carrotIndustries/usbkvm/hw/usbkvm-pro/pool/3d_models/cache/6d752bc3-29b3-45df-8cf2-1e3aacefbcc6/3d_models/passive/capacitor/C_0402_1005Metric.step

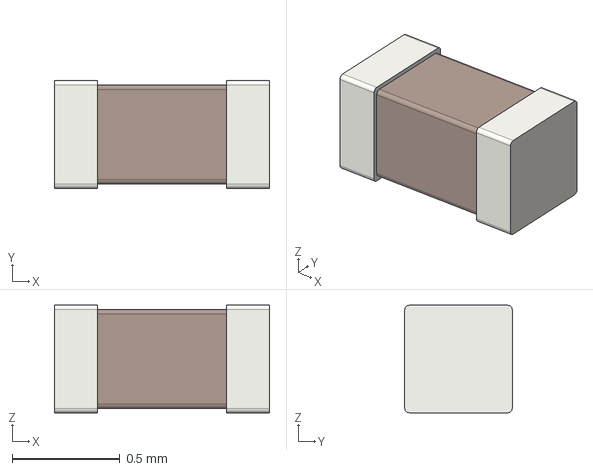
[picture p24: CAD file, 2024-03-15]
hw/usbkvm-pro/pool/3d_models/cache/6d752bc3-29b3-45df-8cf2-1e3aacefbcc6/3d_models/passive/capacitor/C_0402_1005Metric.step
1.00 x 0.5 x 0.5 mm
