carrotIndustries/usbkvm/hw/usbkvm-pro/pool/3d_models/cache/6d752bc3-29b3-45df-8cf2-1e3aacefbcc6/3d_models/passive/capacitor/C_0805_2012Metric.step

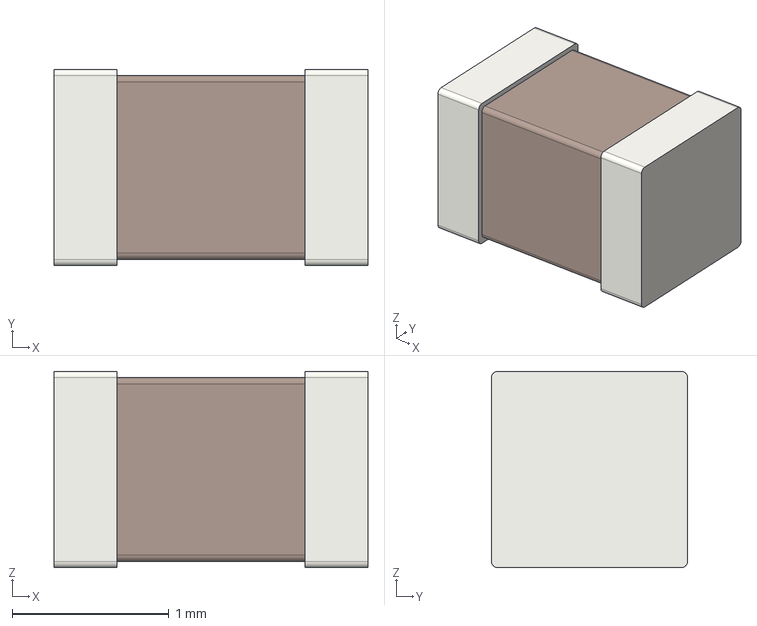
[picture p26: CAD file, 2024-03-15]
hw/usbkvm-pro/pool/3d_models/cache/6d752bc3-29b3-45df-8cf2-1e3aacefbcc6/3d_models/passive/capacitor/C_0805_2012Metric.step
2.00 x 1.25 x 1.25 mm
