carrotIndustries/usbkvm/hw/usbkvm-pro/pool/3d_models/cache/6d752bc3-29b3-45df-8cf2-1e3aacefbcc6/3d_models/ic/so/SOT-363_SC-70-6.step

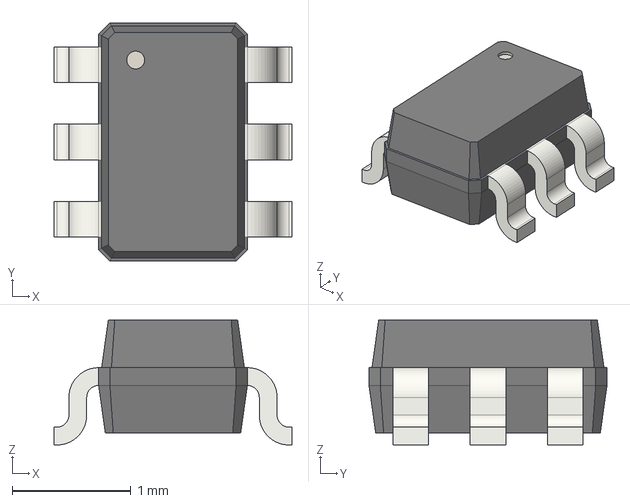
[picture p27: CAD file, 2024-03-15]
hw/usbkvm-pro/pool/3d_models/cache/6d752bc3-29b3-45df-8cf2-1e3aacefbcc6/3d_models/ic/so/SOT-363_SC-70-6.step
2.00 x 2.00 x 1.05 mm
