carrotIndustries/usbkvm/app/src/usbkvm_application.cpp

#include "usbkvm_application.hpp"
#include "main_window.hpp"
#include "about_dialog.hpp"
#include <iostream>
#include <hidapi.h>
#include "util.hpp"
#include "devices_window.hpp"

#ifndef G_OS_WIN32
#include <fcntl.h>
#include <linux/types.h>
#include <linux/input.h>
#include <linux/hidraw.h>
#endif

namespace usbkvm {

UsbKvmApplication::UsbKvmApplication() : Gtk::Application("net.carrotindustries.usbkvm", Gio::APPLICATION_FLAGS_NONE)
{
    add_main_option_entry(Gio::Application::OptionType::OPTION_TYPE_BOOL, "force-firmware-update", 0,
                          "Force firmware update regardless of detected version");
    add_main_option_entry(Gio::Application::OptionType::OPTION_TYPE_INT, "i2c-delay", 0,
                          "Min. I2C transaction interval in us");
    signal_handle_local_options().connect([this](const Glib::RefPtr<Glib::VariantDict> &dict) {
        bool force = false;
        dict->lookup_value("force-firmware-update", force);
        m_force_firmware_update = force;

        gint32 i2c_delay = 0;
        if (dict->lookup_value("i2c-delay", i2c_delay)) {
            if (i2c_delay == 1)
                i2c_delay = 0;
            m_i2c_delay_us = i2c_delay;
        }

        return -1;
    });
}

Glib::RefPtr<UsbKvmApplication> UsbKvmApplication::create()
{
    return Glib::RefPtr<UsbKvmApplication>(new UsbKvmApplication());
}

UsbKvmAppWindow *UsbKvmApplication::create_appwindow()
{
    auto appwindow = UsbKvmAppWindow::create(*this);

    // Make sure that the application runs for as long this window is still
    // open.
    add_window(*appwindow);

    // Gtk::Application::add_window() connects a signal handler to the window's
    // signal_hide(). That handler removes the window from the application.
    // If it's the last window to be removed, the application stops running.
    // Gtk::Window::set_application() does not connect a signal handler, but is
    // otherwise equivalent to Gtk::Application::add_window().

    // Delete the window when it is hidden.
    appwindow->signal_hide().connect(sigc::bind(sigc::mem_fun(*this, &UsbKvmApplication::on_hide_window), appwindow));

    return appwindow;
}

void UsbKvmApplication::on_activate()
{
    if (auto win = get_active_window()) {
        win->present();
        return;
    }
    auto appwindow = create_appwindow();
    appwindow->present();
}


void UsbKvmApplication::on_startup()
{
    // Call the base class's implementation.
    Gtk::Application::on_startup();

    add_action("quit", sigc::mem_fun(*this, &UsbKvmApplication::on_action_quit));
    add_action("about", sigc::mem_fun(*this, &UsbKvmApplication::on_action_about));
    add_action("devices", sigc::mem_fun(*this, &UsbKvmApplication::on_action_devices));

    auto cssp = Gtk::CssProvider::create();
    cssp->load_from_resource("/net/carrotIndustries/usbkvm/usbkvm.css");
    Gtk::StyleContext::add_provider_for_screen(Gdk::Screen::get_default(), cssp,
                                               GTK_STYLE_PROVIDER_PRIORITY_APPLICATION);
    Gtk::IconTheme::get_default()->add_resource_path("/net/carrotIndustries/usbkvm/icons");

    {
        m_monitor = gst_device_monitor_new();
        gst_device_monitor_set_show_all_devices(m_monitor, true);

        auto bus = gst_device_monitor_get_bus(m_monitor);
        gst_device_monitor_add_filter(m_monitor, "Video/Source", NULL);
        gst_bus_add_watch(bus, &UsbKvmApplication::monitor_bus_func, this);
        gst_object_unref(bus);
        gst_device_monitor_start(m_monitor);
    }

    Gtk::Settings::get_default()->property_gtk_menu_bar_accel() = "";

    m_devices_window = DevicesWindow::create(*this);

    signal_shutdown().connect(sigc::mem_fun(*this, &UsbKvmApplication::on_shutdown));
}


void UsbKvmApplication::on_shutdown()
{
    gst_device_monitor_stop(m_monitor);
    gst_object_unref(m_monitor);
    gst_deinit();
}

void UsbKvmApplication::on_hide_window(Gtk::Window *window)
{
    delete window;
}


void UsbKvmApplication::on_action_quit()
{
    // Gio::Application::quit() will make Gio::Application::run() return,
    // but it's a crude way of ending the program. The window is not removed
    // from the application. Neither the window's nor the application's
    // destructors will be called, because there will be remaining reference
    // counts in both of them. If we want the destructors to be called, we
    // must remove the window from the application. One way of doing this
    // is to hide the window. See comment in create_appwindow().
    auto windows = get_windows();
    for (auto win : windows)
        win->close();
}

void UsbKvmApplication::on_action_about()
{
    AboutDialog dia;
    auto win = get_active_window();
    if (win)
        dia.set_transient_for(*win);
    dia.run();
}

void UsbKvmApplication::on_action_devices()
{
    auto win = get_active_window();
    if (win)
        m_devices_window->set_transient_for(*win);
    m_devices_window->present();
}


gboolean UsbKvmApplication::monitor_bus_func(GstBus *bus, GstMessage *message, gpointer pself)
{
    auto self = reinterpret_cast<UsbKvmApplication *>(pself);
    return self->monitor_bus_func(bus, message);
}

static const std::string s_device_name = "USBKVM";

static std::string struct_get_string(const GstStructure *props, const char *name)
{
    if (auto r = gst_structure_get_string(props, name))
        return r;
    else
        return "";
}

struct OpenError : public std::runtime_error {
    using std::runtime_error::runtime_error;
};

#ifdef G_OS_WIN32

static std::string get_path(GstDevice *device)
{
    gchar *device_path;
    g_object_get(G_OBJECT(device), "path", &device_path, NULL);
    std::string r = device_path;
    g_free(device_path);
    return r;
}

static std::string get_hid_bus_info(const std::string &path)
{
    auto x = get_win32_hid_bus_info(path);
    if (x)
        return x.value();
    return "";
}

#else

static std::string get_hid_bus_info(const std::string &path)
{
    auto fd = open(path.c_str(), O_RDWR | O_NONBLOCK);
    if (fd == -1) {
        throw OpenError("can't open " + path + ", " + std::string(strerror(errno)));
        return "";
    }

    char buf[256] = {0};
    auto res = ioctl(fd, HIDIOCGRAWPHYS(256), buf);
    if (res < 0) {
        close(fd);
        return "";
    }
    else {
        close(fd);
        std::string buf_s = buf;
        auto slash_pos = buf_s.find('/');
        if (slash_pos == std::string::npos)
            return "";
        return buf_s.substr(0, slash_pos);
    }
}

static std::string get_path(GstDevice *device)
{
    auto props = gst_device_get_properties(device);
    auto path = struct_get_string(props, "device.path");
    if (!path.size())
        path = struct_get_string(props, "api.v4l2.path");
    gst_structure_free(props);
    return path;
}

#endif

static std::vector<gint> try_parse_dim(GstStructure *structure, const char *field)
{
    {
        int x;
        if (gst_structure_get_int(structure, field, &x))
            return {x};
    }
    {
        std::vector<gint> xs;
        GValueArray *array = nullptr;
        if (gst_structure_get_list(structure, field, &array)) {
            for (size_t i = 0; i < array->n_values; i++) {
                auto it = g_value_array_get_nth(array, i);
                if (it && G_VALUE_HOLDS(it, G_TYPE_INT)) {
                    auto x = g_value_get_int(it);
                    xs.push_back(x);
                }
            }
            g_value_array_free(array);
        }
        return xs;
    }
}

static gboolean handle_cap(GstCapsFeatures *features, GstStructure *structure, gpointer user_data)
{
    std::string name = gst_structure_get_name(structure);
    auto &ress = *(reinterpret_cast<DeviceInfo::ResolutionList *>(user_data));
    if (name == "image/jpeg") {
        std::vector<gint> widths, heights;
        widths = try_parse_dim(structure, "width");
        heights = try_parse_dim(structure, "height");
        for (const auto width : widths) {
            for (const auto height : heights) {
                ress.emplace_back(width, height);
            }
        }
    }
    return true;
}

const std::string UsbKvmApplication::s_recovery = "RECOVERY";


bool UsbKvmApplication::probe_device(const std::string &video_path, const std::string &video_bus_info,
                                     const DeviceInfo::ResolutionList &capture_resolutions)
{
    const auto recovery_mode = video_path == s_recovery;
    if (!recovery_mode) {
        if (!m_video_devices.contains(video_path))
            return false;
        {
            auto &x = m_video_devices.at(video_path);
            if (x++ == 10) {
                auto md = new Gtk::MessageDialog("Can't open HID interface", false, Gtk::MESSAGE_ERROR);
                md->set_secondary_text("didn't find HID device after one second", true);

                md->set_transient_for(*get_active_window());
                md->set_modal(true);
                md->present();
                md->signal_response().connect([md](auto response) { delete md; });
                return false;
            }
        }
    }

    auto devinfos = hid_enumerate(0x534d, 0x2109);
    bool found = false;
    for (const hid_device_info *dev = devinfos; dev != nullptr; dev = dev->next) {
        if (recovery_mode || (dev->product_string && wide_string_to_string(dev->product_string) == s_device_name)) {
            std::string hid_bus_info;
            try {
                hid_bus_info = get_hid_bus_info(dev->path);
            }
            catch (const OpenError &e) {
                auto md = new Gtk::MessageDialog("Can't open HID interface", false, Gtk::MESSAGE_ERROR);
                md->set_secondary_text(std::string(e.what()) + "\nSee <a href='https://github.com/carrotIndustries/usbkvm/blob/main/app/README.md'>github.com/carrotIndustries/usbkvm</a> for troubleshooting.", true);

                md->set_transient_for(*get_active_window());
                md->set_modal(true);
                md->present();
                md->signal_response().connect([md](auto response) { delete md; });
            }
            if (recovery_mode || hid_bus_info == video_bus_info) {
                on_device_added({.video_path = video_path,
                                 .hid_path = dev->path,
                                 .bus_info = hid_bus_info,
                                 .capture_resolutions = capture_resolutions});
                found = true;
                break;
            }
        }
    }
    hid_free_enumeration(devinfos);
    return !found;
}

gboolean UsbKvmApplication::monitor_bus_func(GstBus *bus, GstMessage *message)
{
    GstDevice *device;
    gchar *name;

    switch (GST_MESSAGE_TYPE(message)) {
    case GST_MESSAGE_DEVICE_ADDED: {
        gst_message_parse_device_added(message, &device);
        name = gst_device_get_display_name(device);
        g_print("Device added: %s\n", name);
        std::string name_str = name;
        if (name_str.starts_with(s_device_name)) {
            {
                DeviceInfo::ResolutionList capture_resolutions;
                {
                    auto caps = gst_device_get_caps(device);
                    gst_caps_foreach(caps, &handle_cap, &capture_resolutions);
                    gst_caps_unref(caps);
                }

                std::string video_path = get_path(device);
                std::string video_bus_info;
#ifdef G_OS_WIN32
                {
                    auto x = get_win32_video_bus_info(video_path);
                    if (x)
                        video_bus_info = x.value();
                }
#else
                auto props = gst_device_get_properties(device);
                video_bus_info = struct_get_string(props, "v4l2.device.bus_info");
                if (!video_bus_info.size())
                    video_bus_info = struct_get_string(props, "api.v4l2.cap.bus_info");
                gst_structure_free(props);
#endif

                if (video_path.size() && video_bus_info.size()) {
                    std::cout << "found video " << video_path << " at " << video_bus_info << std::endl;
                    if (m_video_devices.emplace(video_path, 0u).second) {
                        // give the HID device one second to appear
                        Glib::signal_timeout().connect(
                                [this, video_path, video_bus_info, capture_resolutions] {
                                    return probe_device(video_path, video_bus_info, capture_resolutions);
                                },
                                100);
                    }
                    else {
                        std::cout << "ignoring duplicate device " << video_path << std::endl;
                    }
                }
            }
        }
        g_free(name);
        gst_object_unref(device);
    } break;
    case GST_MESSAGE_DEVICE_REMOVED: {
        gst_message_parse_device_removed(message, &device);
        name = gst_device_get_display_name(device);
        auto path = get_path(device);
        std::string name_s = name;
        std::cout << "Device removed: " << name_s << " " << path << std::endl;
        m_video_devices.erase(path);
        on_device_removed(path);
        g_free(name);
        gst_object_unref(device);

    } break;
    default:
        break;
    }

    return G_SOURCE_CONTINUE;
}

void UsbKvmApplication::on_device_added(const DeviceInfo &devinfo)
{
    m_devices.emplace(devinfo.video_path, devinfo);
    m_signal_devices_changed.emit();
    // try to use last window
    for (auto win2 : get_windows()) {
        auto &win = dynamic_cast<UsbKvmAppWindow &>(*win2);
        if (win.get_device_info() == nullptr
            && (win.get_last_bus_info() == devinfo.bus_info || win.get_last_bus_info().empty())) {
            win.set_device(devinfo);
            return;
        }
    }
    // try any free window
    for (auto win2 : get_windows()) {
        auto &win = dynamic_cast<UsbKvmAppWindow &>(*win2);
        if (win.get_device_info() == nullptr) {
            win.set_device(devinfo);
            return;
        }
    }
    // no window, create new
    auto appwindow = create_appwindow();
    appwindow->set_device(devinfo);
    appwindow->present();
}

void UsbKvmApplication::on_device_removed(const std::string &video_path)
{
    for (auto win2 : get_windows()) {
        auto &win = dynamic_cast<UsbKvmAppWindow &>(*win2);
        if (auto info = win.get_device_info()) {
            if (info->video_path == video_path) {
                win.unset_device();
                break;
            }
        }
    }
    m_devices.erase(video_path);
    m_signal_devices_changed.emit();
}

void UsbKvmApplication::update_device_info(const DeviceInfo &info)
{
    if (m_devices.contains(info.video_path)) {
        auto &dev = m_devices.at(info.video_path);
        dev.model = info.model;
        dev.serial = info.serial;
        m_signal_devices_changed.emit();
    }
}

std::vector<const DeviceInfo *> UsbKvmApplication::get_devices() const
{
    std::vector<const DeviceInfo *> r;
    for (auto &[path, dev] : m_devices) {
        r.push_back(&dev);
    }
    return r;
}

void UsbKvmApplication::activate_device(const std::string &video_path)
{
    for (auto win2 : get_windows()) {
        auto &win = dynamic_cast<UsbKvmAppWindow &>(*win2);
        if (auto info = win.get_device_info()) {
            if (info->video_path == video_path) {
                win.present();
                return;
            }
        }
    }
    if (!m_devices.contains(video_path))
        return;
    auto appwindow = create_appwindow();
    appwindow->set_device(m_devices.at(video_path));
    appwindow->present();
}

void UsbKvmApplication::recover_eeprom()
{
    probe_device(s_recovery, s_recovery, {});
}

} // namespace usbkvm
