carrotIndustries/usbkvm/fw/usbkvm/Core/Inc/i2c_msg_app.h

#pragma once
#include "i2c_msg_common.h"

#define I2C_APP_VERSION 7

REQ_ENUM_BEGIN(i2c_req)
    REQ_ENUM_ITEM(I2C_REQ, KEYBOARD_REPORT  ,  1)
    REQ_ENUM_ITEM(I2C_REQ, MOUSE_REPORT     ,  2)
    REQ_ENUM_ITEM(I2C_REQ, ENTER_BOOTLOADER ,  4)
    REQ_ENUM_ITEM(I2C_REQ, GET_STATUS       ,  5)
    REQ_ENUM_ITEM(I2C_REQ, SET_LED          ,  6)
    REQ_ENUM_ITEM(I2C_REQ, FLASH_UNLOCK     ,  7)
    REQ_ENUM_ITEM(I2C_REQ, FLASH_LOCK       ,  8)
    REQ_ENUM_ITEM(I2C_REQ, FLASH_ERASE      ,  9)
    REQ_ENUM_ITEM(I2C_REQ, FLASH_WRITE      , 10)
    REQ_ENUM_ITEM(I2C_REQ, GET_UNIQUE_ID    , 11)
REQ_ENUM_END

typedef struct {
    I2C_REQ_COMMON
    uint8_t mod;
    uint8_t keycode[6];
} i2c_req_keyboard_report_t;

typedef struct {
    I2C_REQ_COMMON
    uint8_t button;
    uint8_t _pad;
    int16_t x;
    int16_t y;
    int8_t h;
    int8_t v;
} i2c_req_mouse_report_t;

typedef struct {
    I2C_RESP_COMMON
    uint8_t success;
} i2c_resp_report_t;

#define I2C_LED_USB (1 << 0)
#define I2C_LED_HID (1 << 1)
#define I2C_LED_HDMI (1 << 2)

typedef struct {
  I2C_REQ_COMMON
  uint8_t mask;
  uint8_t stat;
} i2c_req_set_led_t;

typedef struct {
  I2C_REQ_COMMON;
  uint8_t first_page;
  uint8_t n_pages;
} i2c_req_flash_erase_t;

typedef struct {
  I2C_REQ_COMMON;
  uint16_t offset;
  uint8_t data[16];
} i2c_req_flash_write_t;

typedef union {
    i2c_req_unknown_t unk;
    i2c_req_keyboard_report_t kbd;
    i2c_req_mouse_report_t mouse;
    i2c_req_set_led_t set_led;
    i2c_req_flash_erase_t flash_erase;
    i2c_req_flash_write_t flash_write;
} i2c_req_app_all_t;

#define I2C_STATUS_VGA_CONNECTED (1<<0)

typedef struct {
    I2C_RESP_COMMON
    uint8_t status;
} i2c_resp_status_t;

typedef struct {
    I2C_RESP_COMMON
    uint8_t success;
} i2c_resp_flash_status_t;

typedef struct {
    I2C_RESP_COMMON
    uint16_t _pad;
    uint32_t uid[3];
} i2c_resp_unique_id_t;

typedef union {
    i2c_resp_unknown_t unk;
    i2c_resp_info_t info;
    i2c_resp_status_t status;
    i2c_resp_flash_status_t flash_status;
    i2c_resp_report_t report;
    i2c_resp_unique_id_t unique_id;
} i2c_resp_app_all_t;

DEFINE_XFER(i2c_req_t::KEYBOARD_REPORT  , i2c_req_keyboard_report_t , i2c_resp_report_t    )
DEFINE_XFER(i2c_req_t::MOUSE_REPORT     , i2c_req_mouse_report_t    , i2c_resp_report_t    )
DEFINE_XFER(i2c_req_t::ENTER_BOOTLOADER , i2c_req_unknown_t         , void                 )
DEFINE_XFER(i2c_req_t::GET_STATUS       , i2c_req_unknown_t         , i2c_resp_status_t    )
DEFINE_XFER(i2c_req_t::SET_LED          , i2c_req_set_led_t         , void                 )
DEFINE_XFER(i2c_req_t::GET_UNIQUE_ID    , i2c_req_unknown_t         , i2c_resp_unique_id_t )
