carrotIndustries/usbkvm/app/src/imcu_provider.hpp

#pragma once
#include <string>

namespace usbkvm {

class UsbKvmMcu;

class IMcuProvider {
public:
    virtual UsbKvmMcu *get_mcu() = 0;
    virtual void handle_io_error(const std::string &err) = 0;
};

} // namespace usbkvm
